NikolasKelava/macro-keyboard/firmware/zmk-config/module/src/behavior_encoder_mode_next.c

/*
 * Copyright (c) 2026 The ZMK Contributors
 * SPDX-License-Identifier: MIT
 *
 * Custom ZMK behavior: &enc_mode_next.
 *
 * On press, advances the current profile's encoder mode (volume -> vertical
 * scroll -> horizontal scroll -> volume). Bound to a regular key so the user
 * can change what the AS5600 knob does without switching profile. The mode is
 * per-profile runtime state held in encoder_mode.c; the &enc_dispatch sensor
 * behavior reads it to decide what each tick emits.
 */

#define DT_DRV_COMPAT zmk_behavior_encoder_mode_next

#include <zephyr/device.h>
#include <zephyr/logging/log.h>

#include <drivers/behavior.h>
#include <zmk/behavior.h>

#include "encoder_mode.h"

LOG_MODULE_DECLARE(zmk, CONFIG_ZMK_LOG_LEVEL);

#if DT_HAS_COMPAT_STATUS_OKAY(DT_DRV_COMPAT)

static int on_keymap_binding_pressed(struct zmk_behavior_binding *binding,
                                     struct zmk_behavior_binding_event event) {
    encoder_mode_cycle();
    LOG_DBG("enc_mode_next: new mode %d", encoder_mode_get());
    return ZMK_BEHAVIOR_OPAQUE;
}

static int on_keymap_binding_released(struct zmk_behavior_binding *binding,
                                      struct zmk_behavior_binding_event event) {
    return ZMK_BEHAVIOR_OPAQUE;
}

static const struct behavior_driver_api behavior_encoder_mode_next_driver_api = {
    .binding_pressed = on_keymap_binding_pressed,
    .binding_released = on_keymap_binding_released,
#if IS_ENABLED(CONFIG_ZMK_BEHAVIOR_METADATA)
    .get_parameter_metadata = zmk_behavior_get_empty_param_metadata,
#endif
};

BEHAVIOR_DT_INST_DEFINE(0, NULL, NULL, NULL, NULL, POST_KERNEL,
                        CONFIG_KERNEL_INIT_PRIORITY_DEFAULT,
                        &behavior_encoder_mode_next_driver_api);

#endif /* DT_HAS_COMPAT_STATUS_OKAY(DT_DRV_COMPAT) */
